ras-marques/ImmersiveGloves/CustomPCBs/InDevelopment/tundraIOExpansion/StencilJig/StencilBottom.stl

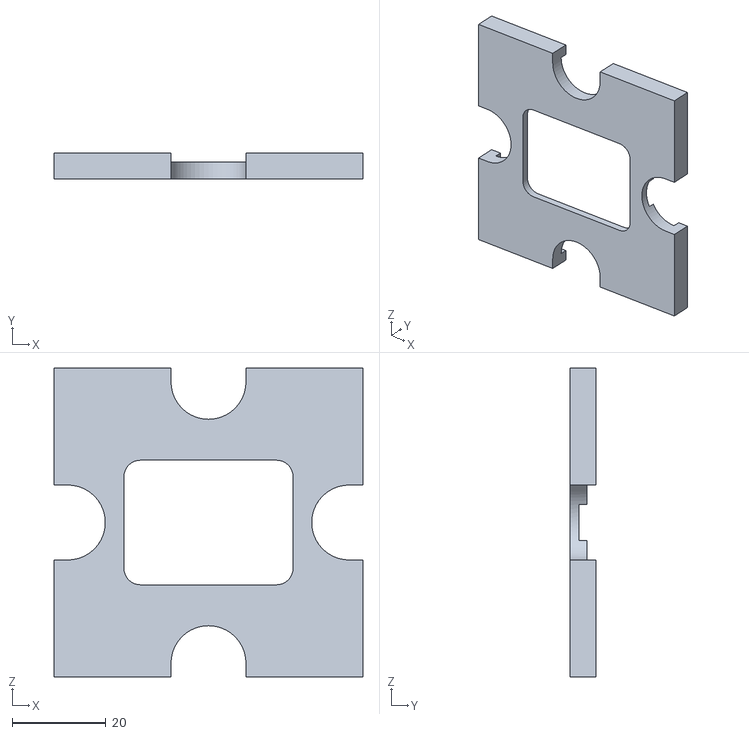
[picture p21: CAD file, 2024-01-13]
CustomPCBs/InDevelopment/tundraIOExpansion/StencilJig/StencilBottom.stl
66.0 x 5.65 x 66.0
