ras-marques/ImmersiveGloves/3DPrintingFiles/ReadyToTest/BackPlate/BackPlate.stl

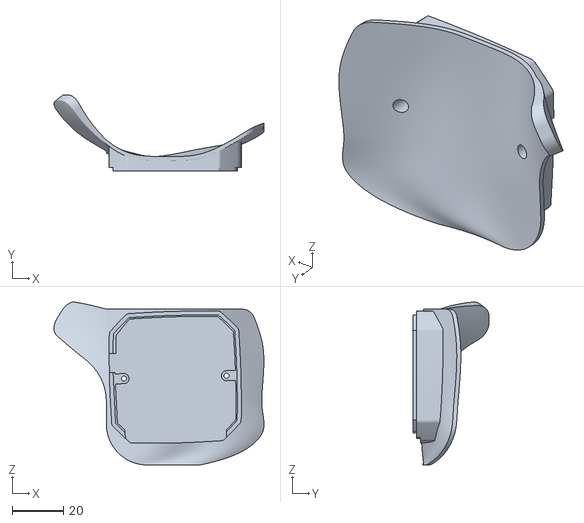
[picture p22: CAD file, 2023-12-02]
3DPrintingFiles/ReadyToTest/BackPlate/BackPlate.stl
82.0 x 29.8 x 63.7
