ras-marques/ImmersiveGloves/CustomPCBs/ComponentLibraries/3dmodels/6-TSOP.STEP

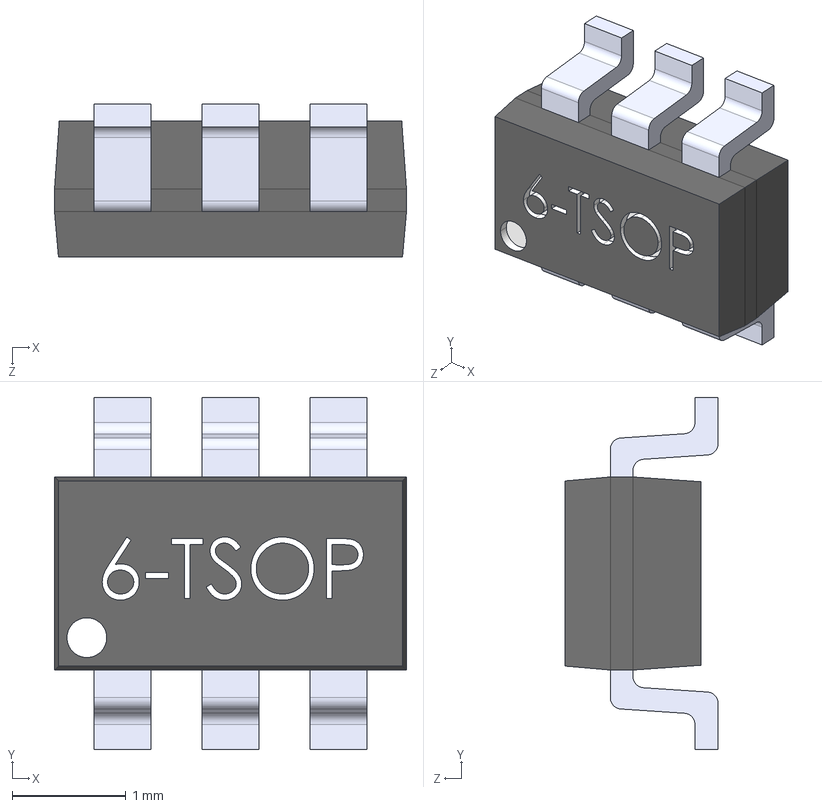
[picture p23: CAD file, 2024-02-26]
CustomPCBs/ComponentLibraries/3dmodels/6-TSOP.STEP
3.10 x 3.10 x 1.35 mm
