ras-marques/ImmersiveGloves/3DPrintingFiles/ReadyToTest/BackPlate/IMUHardPoint.stl

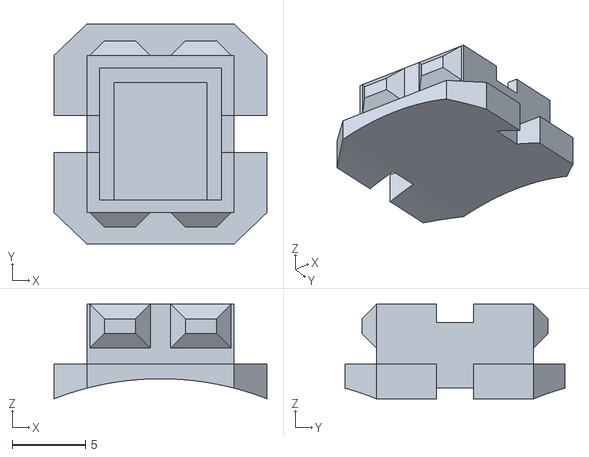
[picture p24: CAD file, 2023-12-02]
3DPrintingFiles/ReadyToTest/BackPlate/IMUHardPoint.stl
14.6 x 15.0 x 6.48
