ras-marques/ImmersiveGloves/CustomPCBs/ComponentLibraries/3dmodels/BSS138BKS,115.stp

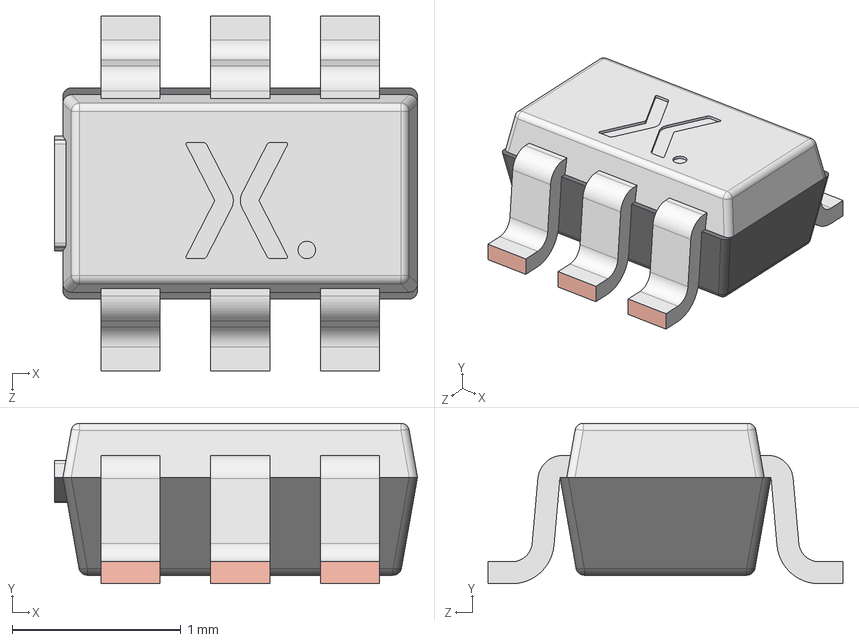
[picture p25: CAD file, 2024-02-26]
CustomPCBs/ComponentLibraries/3dmodels/BSS138BKS,115.stp
2.15 x 0.95 x 2.10 mm
SOT353 Lower body
SOT353 Lead x 6
SOT353 Upper body
