ras-marques/ImmersiveGloves/CustomPCBs/ComponentLibraries/3dmodels/ICM-20948.step

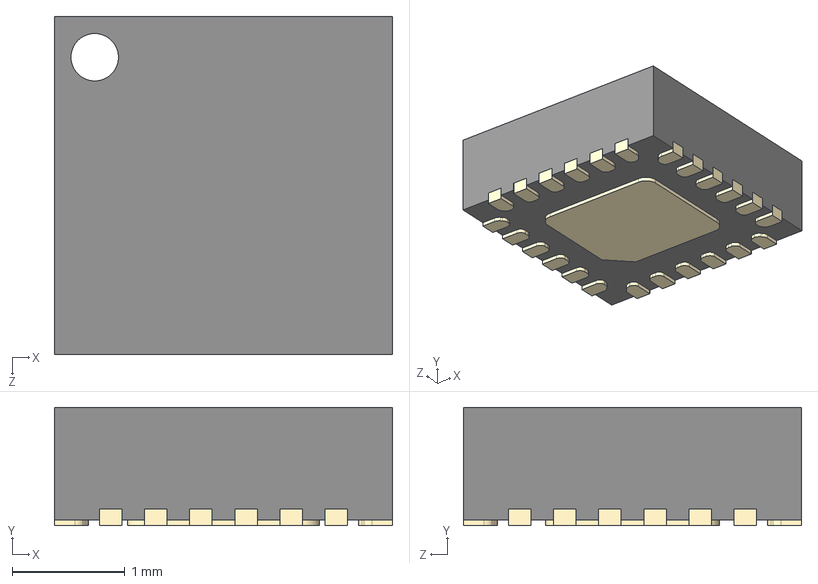
[picture p26: CAD file, 2024-02-26]
CustomPCBs/ComponentLibraries/3dmodels/ICM-20948.step
3.00 x 1.05 x 3.00 mm
