ras-marques/ImmersiveGloves/CustomPCBs/ComponentLibraries/3dmodels/User Library-SOT23-3.step

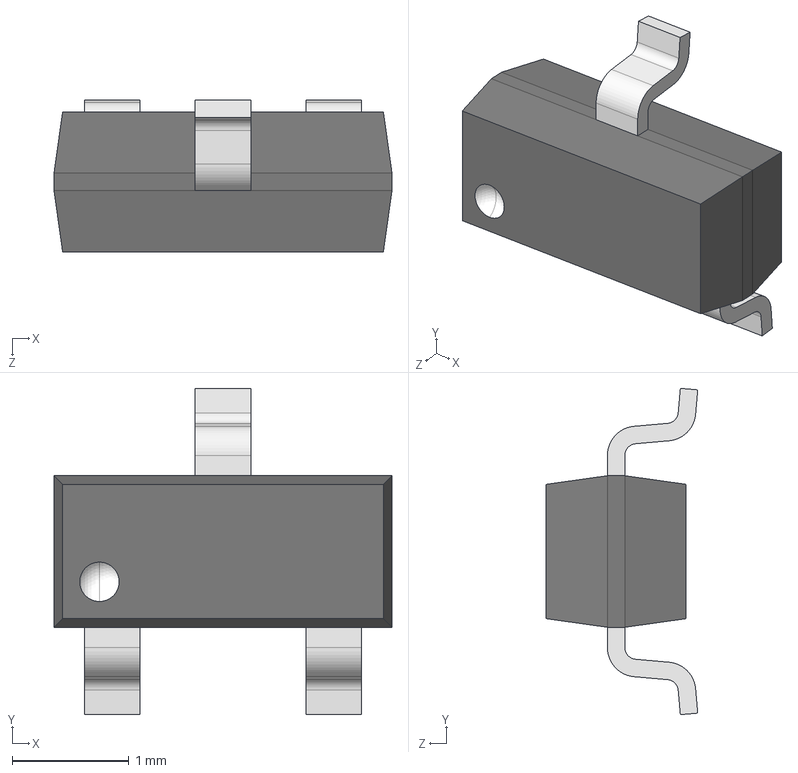
[picture p27: CAD file, 2024-02-26]
CustomPCBs/ComponentLibraries/3dmodels/User Library-SOT23-3.step
2.90 x 2.80 x 1.30 mm
