ras-marques/ImmersiveGloves/CustomPCBs/ComponentLibraries/3dmodels/User Library-TSSOP-6 (SOT-23-6 PITCH 0_65).STEP

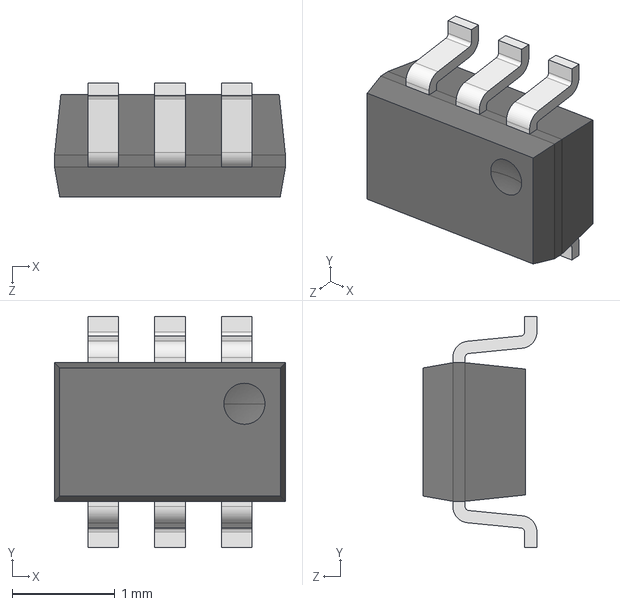
[picture p28: CAD file, 2024-02-26]
CustomPCBs/ComponentLibraries/3dmodels/User Library-TSSOP-6 (SOT-23-6 PITCH 0_65).STEP
2.25 x 2.25 x 1.11 mm
pin_TSSOP_tssop6_1 x 6
body_TSSOP-6_TSSOP5_1
