ras-marques/ImmersiveGloves/CustomPCBs/ComponentLibraries/3dmodels/HMC5883L-TR.step

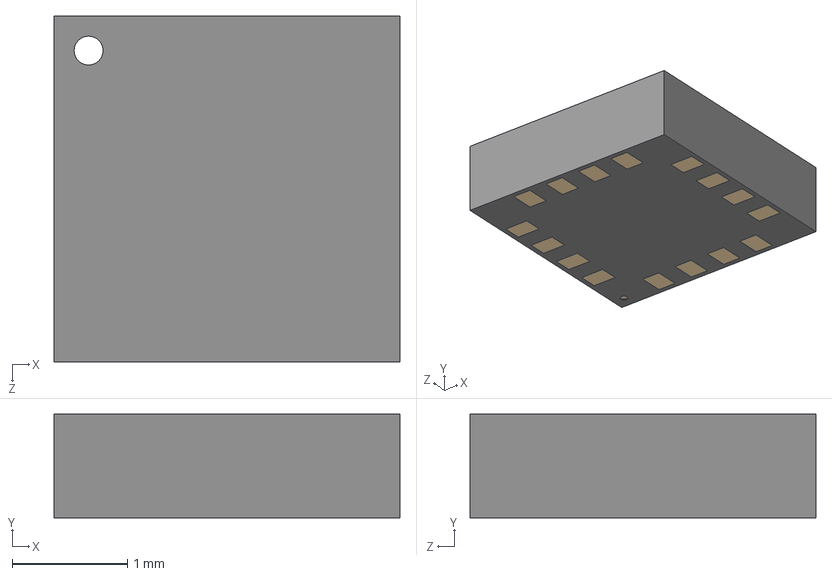
[picture p29: CAD file, 2024-02-26]
CustomPCBs/ComponentLibraries/3dmodels/HMC5883L-TR.step
3.00 x 0.9 x 3.00 mm
