ras-marques/ImmersiveGloves/CustomPCBs/ComponentLibraries/3dmodels/BSS138W-7-F.step

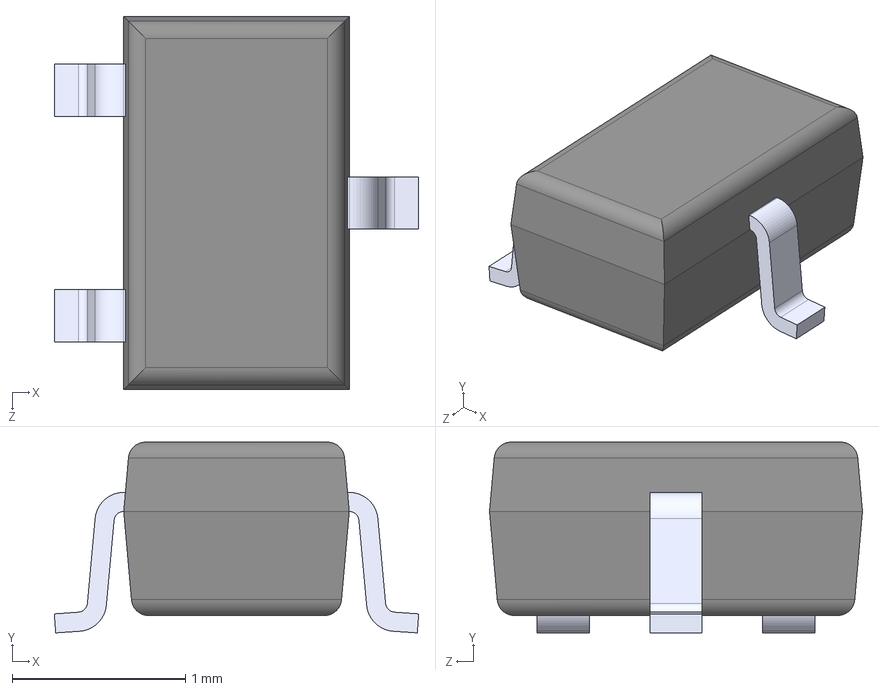
[picture p30: CAD file, 2024-02-25]
CustomPCBs/ComponentLibraries/3dmodels/BSS138W-7-F.step
2.10 x 1.10 x 2.15 mm
