ras-marques/ImmersiveGloves/CustomPCBs/ComponentLibraries/3dmodels/SM04B-SRSS-TB.STEP

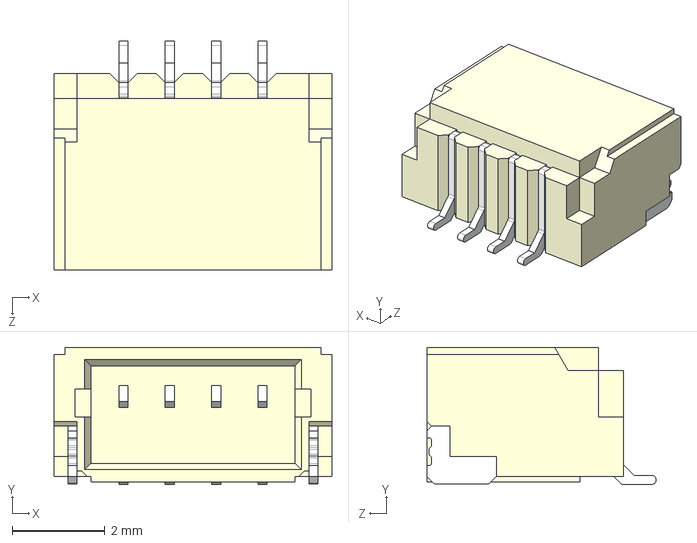
[picture p31: CAD file, 2024-02-16]
CustomPCBs/ComponentLibraries/3dmodels/SM04B-SRSS-TB.STEP
6.00 x 2.96 x 4.95 mm
