ras-marques/ImmersiveGloves/CustomPCBs/ComponentLibraries/3dmodels/LGA14-L_2P59X3P1X0P5_STM.step

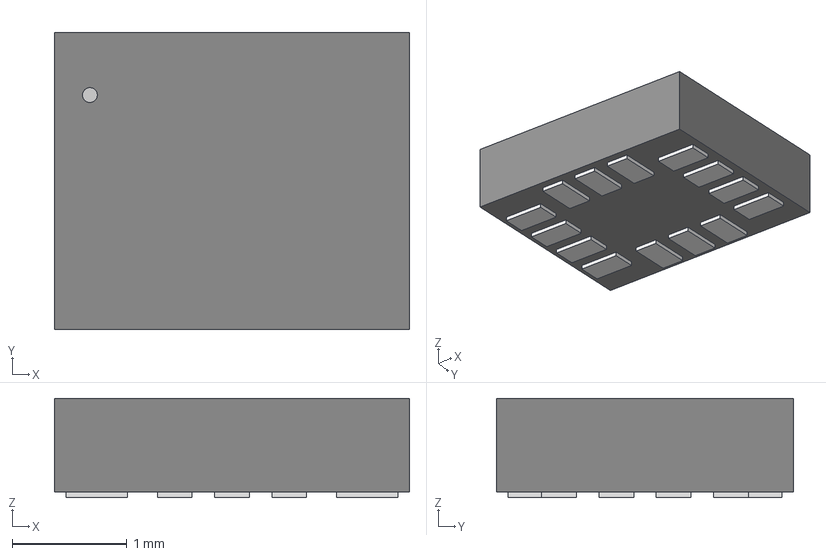
[picture p32: CAD file, 2024-02-16]
CustomPCBs/ComponentLibraries/3dmodels/LGA14-L_2P59X3P1X0P5_STM.step
3.10 x 2.59 x 0.866 mm
