ras-marques/ImmersiveGloves/rp2040Firmware/code.py

import array
import board
import busio
from adafruit_bno08x.i2c import BNO08X_I2C
from adafruit_bno08x import BNO_REPORT_LINEAR_ACCELERATION   # gives the acceleration with the gravity removed
from adafruit_bno08x import BNO_REPORT_ROTATION_VECTOR       # gives a quaternion from sensor fusion, including the magnetometer data

from adafruit_bno08x import BNO_REPORT_ACCELEROMETER
from adafruit_bno08x import BNO_REPORT_MAGNETOMETER
from adafruit_bno08x import BNO_REPORT_GYROSCOPE

# import pyquaternion
from ulab import numpy as np
import time
import rp2pio
import adafruit_pioasm
import bitbangio
import digitalio
import usb_cdc

serial = usb_cdc.data

assembled = adafruit_pioasm.assemble("""
.program spi_slave
.wrap_target:
    set x, 31
    pull
loop:
    wait 0 pin 1
    wait 0 pin 2
    out pins 1
    wait 1 pin 2
    jmp x-- loop
.wrap
""")

sm = rp2pio.StateMachine(
    assembled,
    frequency=0,
    first_out_pin=board.GP15,
    out_pin_count=1,
    first_in_pin=board.GP12,
    in_pin_count=3,
    out_shift_right=False
)

print(sm.frequency)

# confirmed ok
class Quaternion:
    def __init__(self, w, x, y, z):
        self.w = w
        self.x = x
        self.y = y
        self.z = z
    
    def printMe(self):
        print(str(self.w) + " " + str(self.x) + " " + str(self.y) + " " + str(self.z))
    
    def rotateBy(rotationQuaternion):
        return quaternion_multiply(rotationQuaternion, self)
    
    def getRelativeTo(referenceQuaternion):
        return quaternion_multiply(referenceQuaternion, quaternion_conjugate(self))
        

# confirmed ok
def quaternion_conjugate(q):
    return Quaternion(q.w, -q.x, -q.y, -q.z)

# confirmed ok
def quaternion_multiply(q1, q2):
    w1, x1, y1, z1 = q1.w, q1.x, q1.y, q1.z
    w2, x2, y2, z2 = q2.w, q2.x, q2.y, q2.z

    # Calculate the resulting quaternion components
    w = w1 * w2 - x1 * x2 - y1 * y2 - z1 * z2
    x = w1 * x2 + x1 * w2 + y1 * z2 - z1 * y2
    y = w1 * y2 - x1 * z2 + y1 * w2 + z1 * x2
    z = w1 * z2 + x1 * y2 - y1 * x2 + z1 * w2

    return Quaternion(w, x, y, z)

def getCurl(q):
    return np.arctan2(2 * (q.x * q.w - q.y * q.z), 1 - 2 * (q.x * q.x + q.y * q.y))
def getSplay(q):
    return np.arctan2(2 * (q.x * q.y + q.z * q.w), 1 - 2 * (q.y * q.y + q.z * q.z))
def getRoll(q):
    return np.arctan2(2 * (q.y * q.z + q.w * q.x), 1 - 2 * (q.x * q.x + q.y * q.y))

def quaternion_rotation_matrix(Q):
    """
    Covert a quaternion into a full three-dimensional rotation matrix.
 
    Input
    :param Q: A 4 element array representing the quaternion (q0,q1,q2,q3) 
 
    Output
    :return: A 3x3 element matrix representing the full 3D rotation matrix. 
             This rotation matrix converts a point in the local reference 
             frame to a point in the global reference frame.
    """
    # Extract the values from Q
    q0 = Q.w
    q1 = Q.x
    q2 = Q.y
    q3 = Q.z
     
    # First row of the rotation matrix
    r00 = 2 * (q0 * q0 + q1 * q1) - 1
    r01 = 2 * (q1 * q2 - q0 * q3)
    r02 = 2 * (q1 * q3 + q0 * q2)
     
    # Second row of the rotation matrix
    r10 = 2 * (q1 * q2 + q0 * q3)
    r11 = 2 * (q0 * q0 + q2 * q2) - 1
    r12 = 2 * (q2 * q3 - q0 * q1)
     
    # Third row of the rotation matrix
    r20 = 2 * (q1 * q3 - q0 * q2)
    r21 = 2 * (q2 * q3 + q0 * q1)
    r22 = 2 * (q0 * q0 + q3 * q3) - 1
     
    # 3x3 rotation matrix
    rot_matrix = np.array([[r00, r01, r02],
                           [r10, r11, r12],
                           [r20, r21, r22]])
                            
    return rot_matrix

def rotationMatrixToEulerAngles(R) :
    sy = np.sqrt(R[0,0] * R[0,0] +  R[1,0] * R[1,0])
 
    singular = sy < 1e-6
 
    if  not singular :
        x = np.arctan2(R[2,1] , R[2,2])
        y = np.arctan2(-R[2,0], sy)
        z = np.arctan2(R[1,0], R[0,0])
    else :
        x = np.arctan2(-R[1,2], R[1,1])
        y = np.arctan2(-R[2,0], sy)
        z = 0
 
    return np.array([x*180/3.14, y*180/3.14, z*180/3.14])

def quaternionFromAngle(angle, axis):
    # angle is in radians, x axis is 0, y axis is 1, z axis is 2
    if axis == 0:
        return Quaternion(np.cos(angle/2),np.sin(angle/2),0,0)
    if axis == 1:
        return Quaternion(np.cos(angle/2),0,np.sin(angle/2),0)
    if axis == 2:
        return Quaternion(np.cos(angle/2),0,0,np.sin(angle/2))

thumbActive = False
indexActive = False
middleActive = False
ringActive = False
pinkyActive = False

i2c_0 = 0
i2c_1 = 0
i2c_2 = 0
i2c_3 = 0
i2c_4 = 0
i2c_5 = 0
bnoRef = 0
bnoThumb = 0
bnoIndex = 0
bnoMiddle = 0
bnoRing = 0
bnoPinky = 0

#i2c_0 = busio.I2C(board.GP5, board.GP4, frequency = 400000, timeout = 8000)
#i2c_1 = busio.I2C(board.GP7, board.GP6, frequency = 400000, timeout = 8000)

# bnoRef = BNO08X_I2C(i2c_0, None, 0x4A, False)
# bnoRef.enable_feature(BNO_REPORT_ROTATION_VECTOR)
# bnoRef.enable_feature(BNO_REPORT_LINEAR_ACCELERATION)

#bnoRef.enable_feature(BNO_REPORT_ACCELEROMETER)
#bnoRef.enable_feature(BNO_REPORT_GYROSCOPE)
#bnoRef.enable_feature(BNO_REPORT_MAGNETOMETER)

if thumbActive:
    bnoThumb = BNO08X_I2C(i2c_0, None, 0x4A)
    bnoThumb.enable_feature(BNO_REPORT_ROTATION_VECTOR)
    bnoThumb.enable_feature(BNO_REPORT_LINEAR_ACCELERATION)
if indexActive:
    bnoIndex = BNO08X_I2C(i2c_1, None, 0x4B)
    bnoIndex.enable_feature(BNO_REPORT_ROTATION_VECTOR)
if middleActive:
    bnoMiddle = BNO08X_I2C(i2c_1, None, 0x4A)
    bnoMiddle.enable_feature(BNO_REPORT_ROTATION_VECTOR)
if ringActive:
    i2c_2_bitbanged = bitbangio.I2C(board.GP4, board.GP5, frequency = 400000, timeout = 8000)
    bnoRing = BNO08X_I2C(i2c_2_bitbanged, None, 0x4B)
    bnoRing.enable_feature(BNO_REPORT_ROTATION_VECTOR)
if pinkyActive:
    i2c_3_bitbanged = bitbangio.I2C(board.GP0, board.GP1, frequency = 400000, timeout = 8000)
    bnoPinky = BNO08X_I2C(i2c_3_bitbanged, None, 0x4B)
    bnoPinky.enable_feature(BNO_REPORT_ROTATION_VECTOR)

spi_protocol_rev = 1
frame_id = 0
report_mode = 3         # MI_PROTOCOL_REVISION_GENERIC
status = 0              # 0 normal, 1 bootloader
input_data_length = 15  # 15 bytes, 120 bits, see a bit below
backchannel_length = 0  # only for RX, probably for haptics that I am not using yet (YET!)
event_data_length = 0   # only for RX, probably for haptics that I am not using yet (YET!)
reserved = 0

thumb_axis = 0             # 10  0
index_axis = 512             # 10  10
middle_axis = 512            # 10  20
ring_axis = 0              # 10  30
pinky_axis = 0             # 10  40
thumb_splay_axis = 0       # 10  50
index_splay_axis = 0       # 10  60
middle_splay_axis = 0      # 10  70
ring_splay_axis = 0        # 10  80
pinky_splay_axis = 0       # 10  90
joystick_x = 0             # 10  100
joystick_y = 0             # 10  110
joystickIsEnabled = False  #  1  120

# 120 bits are 15 bytes

first_header_32bits  = (spi_protocol_rev << 24) + (frame_id << 16) + (report_mode << 8) + (status << 0)
second_header_32bits = (input_data_length << 24) + (backchannel_length << 16) + (event_data_length << 8) + (reserved << 0)

# during my tests, for some reason the finger curl was only working if the reference IMU quaternion is the one in the definition below.
# so for everything to work, I define the quaternion below and rotate everything to this coordinate frame.
# for that, I take the relative quaternion from the reference IMU to this quaternion and then use this relative quaternion to rotate every IMU into this reference frame
# then, finally, I do all my calculations.
handQuaternionThatWorks = Quaternion(np.sqrt(2)/2,0,0,-np.sqrt(2)/2)

# for the thumb movement, I needed to get a first neutral position from which to take rotations
# the relative rotation to the reference IMU is represented by the quaternion below, taken experimentally
thumbNeutralToHandQuaternion = Quaternion(0.623351, 0.0097146, 0.754592, 0.204794)

# for the joystick emulation, I need a neutral rotation from which to take roll and pitch and map it into joystick values
# the relative rotation to the reference IMU is represented by the quaternion below, taken experimentally
thumbNeutralJoystickToHandQuaternion = Quaternion(0.586889, -0.168701, 0.779479, 0.140207)

# for splay, I took measurements of the results of my calculations and the splay angle results are as follows:
# finger   min  rest  max
# index    -22   18    35
# middle   -11    4    28
# ring     -14   -5    14
# pinky    -40  -25    -2

refAccelTime = time.monotonic()
thumbAccelTime = time.monotonic()

joystick_enabled = digitalio.DigitalInOut(board.GP10)
joystick_enabled.pull = digitalio.Pull.UP

#################################
# SENSOR FUSION BENCHMARK START #
#################################
def TO_RAD(x):
    return x * 0.01745329252 # *pi/180
def TO_DEG(x):
    return x * 57.2957795131 # *180/pi

# Multiply two 3x3 matrices: out = a * b
def Matrix_Multiply(a, b):
    return np.dot(a,b)

# Adds two vectors
def Vector_Add(v1, v2):
    return v1+v2

# Computes the dot product of two vectors
def Vector_Dot_Product(v1, v2):
    return np.dot(v1,v2)

def Vector_Cross_Product(v1, v2):
    out = np.empty([3])
    out[0] = (v1[1] * v2[2]) - (v1[2] * v2[1])
    out[1] = (v1[2] * v2[0]) - (v1[0] * v2[2])
    out[2] = (v1[0] * v2[1]) - (v1[1] * v2[0])
    return out

# Multiply the vector by a scalar
def Vector_Scale(v, scale):
    return v*scale
# 
# # Init rotation matrix using euler angles
# def init_rotation_matrix(yaw, pitch, roll):
#     m = np.empty([3, 3])
#     c1 = np.cos(roll)
#     s1 = np.sin(roll)
#     c2 = np.cos(pitch)
#     s2 = np.sin(pitch)
#     c3 = np.cos(yaw)
#     s3 = np.sin(yaw)
#     # Euler angles, right-handed, intrinsic, XYZ convention
#     # (which means: rotate around body axes Z, Y', X'')
#     m[0][0] = c2 * c3
#     m[0][1] = c3 * s1 * s2 - c1 * s3
#     m[0][2] = s1 * s3 + c1 * c3 * s2
# 
#     m[1][0] = c2 * s3
#     m[1][1] = c1 * c3 + s1 * s2 * s3
#     m[1][2] = c1 * s2 * s3 - c3 * s1
# 
#     m[2][0] = -s2
#     m[2][1] = c2 * s1
#     m[2][2] = c1 * c2
# 
#     return m
# 
# def read_sensors():
#     global accel_xyz
#     global gyro_xyz
#     global magn_xyz
#     accel_xyz = bnoRef.acceleration
#     gyro_xyz = bnoRef.gyro
#     magn_xyz = bnoRef.magnetic
# 
# def reset_sensor_fusion():
#     global DCM_Matrix
#     global pitch
#     global roll
#     global MAG_Heading
#     global yaw
#     global DCM_Matrix
#     global timer
# 
#     xAxis = [1, 0, 0]
# 
#     read_sensors()
#     timer = time.monotonic()
# 
#     # GET PITCH
#     # Using y-z-plane-component/x-component of gravity vector
#     pitch = -np.arctan2(accel_xyz[0], np.sqrt(accel_xyz[1] * accel_xyz[1] + accel_xyz[2] * accel_xyz[2]))
#     # GET ROLL
#     # Compensate pitch of gravity vector
#     temp1 = Vector_Cross_Product(accel_xyz, xAxis)
#     temp2 = Vector_Cross_Product(xAxis, temp1)
#     # Normally using x-z-plane-component/y-component of compensated gravity vector
#     # roll = atan2(temp2[1], sqrt(temp2[0] * temp2[0] + temp2[2] * temp2[2]))
#     # Since we compensated for pitch, x-z-plane-component equals z-component:
#     roll = np.arctan2(temp2[1], temp2[2])
# 
#     # GET YAW
#     Compass_Heading()
#     yaw = MAG_Heading
# 
#     # Init rotation matrix
#     DCM_Matrix = init_rotation_matrix(yaw, pitch, roll)
# 
# def compensate_gyro_offset():
#     global gyro_xyz
#     gyro_xyz = list(gyro_xyz)
#     gyro_xyz[0] = gyro_xyz[0] - GYRO_AVERAGE_OFFSET_X
#     gyro_xyz[1] = gyro_xyz[1] - GYRO_AVERAGE_OFFSET_Y
#     gyro_xyz[2] = gyro_xyz[2] - GYRO_AVERAGE_OFFSET_Z
# 
# def Compass_Heading():
#     global MAG_Heading
#     
#     cos_roll = np.cos(roll)
#     sin_roll = np.sin(roll)
#     cos_pitch = np.cos(pitch)
#     sin_pitch = np.sin(pitch)
# 
#     # Tilt compensated magnetic field X
#     mag_x = magn_xyz[0] * cos_pitch + magn_xyz[1] * sin_roll * sin_pitch + magn_xyz[2] * cos_roll * sin_pitch
#     # Tilt compensated magnetic field Y
#     mag_y = magn_xyz[1] * cos_roll - magn_xyz[2] * sin_roll
#     # Magnetic Heading
#     MAG_Heading = np.arctan2(-mag_y, mag_x)
#     # MAG_Heading = 0
# 
# def Matrix_update():
#     global Omega
#     global Omega_Vector
#     global gyro_xyz
#     global DCM_Matrix
#     global Temporary_Matrix
#     
#     # gyro_xyz[0] = TO_RAD(gyro_xyz[0]*GYRO_GAIN)
#     # gyro_xyz[1] = TO_RAD(gyro_xyz[1]*GYRO_GAIN)
#     # gyro_xyz[2] = TO_RAD(gyro_xyz[2]*GYRO_GAIN)
#     # gyro_xyz[0] = TO_RAD(gyro_xyz[0])
#     # gyro_xyz[1] = TO_RAD(gyro_xyz[1])
#     # gyro_xyz[2] = TO_RAD(gyro_xyz[2])
# 
#     Update_Matrix = np.empty([3,3])
# 
#     Omega = Vector_Add(gyro_xyz, Omega_I) # adding proportional term calculated in Drift_Correction()
#     Omega_Vector = Vector_Add(Omega, Omega_P) # adding Integrator term calculated in Drift_Correction()
# 
#     #Ver equacoes 15 16 e 17 no paper Direction Cosine Matrix IMU: Theory - William Premerlani and Paul Bizard
#     #Omega_Vector e o vetor do giroscopio com correcao ao drift
#     Update_Matrix[0][0] =0
#     Update_Matrix[0][1]=-G_Dt*Omega_Vector[2] # -z
#     Update_Matrix[0][2]=G_Dt*Omega_Vector[1] # y
#     Update_Matrix[1][0]=G_Dt*Omega_Vector[2] # z
#     Update_Matrix[1][1]=0
#     Update_Matrix[1][2]=-G_Dt*Omega_Vector[0] # -x
#     Update_Matrix[2][0]=-G_Dt*Omega_Vector[1] #-y
#     Update_Matrix[2][1]=G_Dt*Omega_Vector[0] # x
#     Update_Matrix[2][2]=0
# 
#     Temporary_Matrix = Matrix_Multiply(DCM_Matrix,Update_Matrix)
#     DCM_Matrix = DCM_Matrix + Temporary_Matrix
# 
# def Normalize():  # confirmei pelo paper e esta bem
#     temporary = np.empty([3, 3])
# 
#     error = -Vector_Dot_Product(DCM_Matrix[0], DCM_Matrix[1]) * .5  # eq.19
# 
#     temporary[0] = Vector_Scale(DCM_Matrix[1], error)  # eq.19
#     temporary[1] = Vector_Scale(DCM_Matrix[0], error)  # eq.19
# 
#     temporary[0] = Vector_Add(temporary[0], DCM_Matrix[0])  # eq.19
#     temporary[1] = Vector_Add(temporary[1], DCM_Matrix[1])  # eq.19
# 
#     temporary[2] = Vector_Cross_Product(temporary[0], temporary[1])  # c= a x b //eq.20
# 
#     renorm = .5 * (3 - Vector_Dot_Product(temporary[0], temporary[0]))  # eq.21
#     DCM_Matrix[0] = Vector_Scale(temporary[0], renorm)
# 
#     renorm = .5 * (3 - Vector_Dot_Product(temporary[1], temporary[1]))  # eq.21
#     DCM_Matrix[1] = Vector_Scale(temporary[1], renorm)
# 
#     renorm = .5 * (3 - Vector_Dot_Product(temporary[2], temporary[2]))  # eq.21
#     DCM_Matrix[2] = Vector_Scale(temporary[2], renorm)
# 
# def Drift_correction():  # AINDA NAO ACABEI DE PORTAR PARA PYTHON!!!
#     # Global variables
#     global Omega_P
#     global Omega_I
#     global errorRollPitch
#     global errorYaw
#     
#     # Compensation the Roll, Pitch and Yaw drift.
#     # Scaled_Omega_P
#     # Scaled_Omega_I
#     # Accel_magnitude
#     # Accel_weight
# 
#     # *****Roll and Pitch***************
# 
#     # Calculate the magnitude of the accelerometer vector
#     Accel_magnitude = np.sqrt(accel_xyz[0] * accel_xyz[0] + accel_xyz[1] * accel_xyz[1] + accel_xyz[2] * accel_xyz[2])
# 
#     # Dynamic weighting of accelerometer info (reliability filter)
#     # Weight for accelerometer info (<0.5G = 0.0, 1G = 1.0 , >1.5G = 0.0)
#     accel_test = 1 - 2 * abs(1 - Accel_magnitude)
#     if accel_test > 1:
#         Accel_weight = 1
#     elif accel_test < 0:
#         Accel_weight = 0
#     else:
#         Accel_weight = accel_test
# 
#     errorRollPitch = Vector_Cross_Product(accel_xyz, DCM_Matrix[2])  # adjust the ground of reference
#     Omega_P = Vector_Scale(errorRollPitch, Kp_ROLLPITCH * Accel_weight)
# 
#     Scaled_Omega_I = Vector_Scale(errorRollPitch, Ki_ROLLPITCH * Accel_weight)
#     Omega_I = Vector_Add(Omega_I, Scaled_Omega_I)
# 
#     # *****YAW***************
#     # We make the gyro YAW drift correction based on compass magnetic heading
# 
#     mag_heading_x = np.cos(MAG_Heading)
#     mag_heading_y = np.sin(MAG_Heading)
#     errorCourse = (DCM_Matrix[0][0] * mag_heading_y) - (DCM_Matrix[1][0] * mag_heading_x)  # Calculating YAW error
#     errorYaw = Vector_Scale(DCM_Matrix[2], errorCourse)  # Applys the yaw correction to the XYZ rotation of the aircraft, depeding the position.
# 
#     Scaled_Omega_P = Vector_Scale(errorYaw, Kp_YAW)  # .01proportional of YAW.
#     Omega_P = Vector_Add(Omega_P, Scaled_Omega_P)  # Adding  Proportional.
# 
#     Scaled_Omega_I = Vector_Scale(errorYaw, Ki_YAW)  # .00001Integrator
#     Omega_I = Vector_Add(Omega_I, Scaled_Omega_I)  # adding integrator to the Omega_I
# 
# def Euler_angles():
#     global pitch
#     global roll
#     global yaw
# 
#     global pitch_deg
#     global roll_deg
#     global yaw_deg
#     
#     # Vem das identidades trigonometricas da matriz de rotacao: Direct Cosine Matrix (DCM)
#     # Ja confirmei, esta certo, nao perder tempo aqui, ver como a DCM_Matrix e construida antes
#     pitch = -np.asin(DCM_Matrix[2][0])
#     roll = np.arctan2(DCM_Matrix[2][1],DCM_Matrix[2][2])
#     yaw = np.arctan2(DCM_Matrix[1][0],DCM_Matrix[0][0])
# 
#     pitch_deg = TO_DEG(pitch)
#     roll_deg = TO_DEG(roll)
#     yaw_deg = TO_DEG(yaw)
# 
# def print_angles():
#     print("yaw   = %.0f" % yaw_deg)
#     print("pitch = %.0f" % pitch_deg)
#     print("roll  = %.0f" % roll_deg)
#     print("")
# 
# accel_xyz = np.empty([3])
# gyro_xyz = np.empty([3])
# magn_xyz = np.empty([3])
# MAG_Heading = 0
# 
# gyro_offset = np.empty([3])
# for i in range(0, 63):
#     gyro_result = bnoRef.gyro
#     gyro_offset[0] += gyro_result[0]
#     gyro_offset[1] += gyro_result[1]
#     gyro_offset[2] += gyro_result[2]
# 
# GYRO_AVERAGE_OFFSET_X = gyro_offset[0] * 0.015625  # 1/64
# GYRO_AVERAGE_OFFSET_Y = gyro_offset[1] * 0.015625  # 1/64
# GYRO_AVERAGE_OFFSET_Z = gyro_offset[2] * 0.015625  # 1/64
# 
# #DCM parameters
# Kp_ROLLPITCH = 0.02
# Ki_ROLLPITCH = 0.00002
# Kp_YAW = 1.2
# Ki_YAW = 0.00002
# 
# # DCM variables
# MAG_Heading = 0
# #Accel_Vector = np.empty([3]) # Store the acceleration in a vector
# #Gyro_Vector = np.empty([3]) # Store the gyros turn rate in a vector
# Omega_Vector = np.zeros(3) # Corrected Gyro_Vector data
# Omega_P = np.zeros(3) # Omega Proportional correction
# Omega_I = np.zeros(3) # Omega Integrator
# Omega = np.zeros(3)
# errorRollPitch = np.empty([3])
# errorYaw = np.empty([3])
# DCM_Matrix = np.array([[1,0,0],[0,1,0],[0,0,1]])
# Temporary_Matrix = np.empty([3,3])
# 
# reset_sensor_fusion()

timer = time.monotonic_ns()/1000000
# while True:
#     if time.monotonic_ns()/1000000 - timer >= 20:  # Main loop runs at 50Hz
#         timer_old = timer
#         timer = time.monotonic_ns()/1000000
#         if timer > timer_old:
#             G_Dt = (timer - timer_old) / 1000.0  # Real time of loop run. We use this on the DCM algorithm (gyro integration time)
#         else:
#             G_Dt = 0
#         
#         read_sensors()
#         secondTimer = time.monotonic_ns()/1000000
#         
#         for i in range(6):        
#             #pitch_test = -np.arctan2(accel_xyz[0], np.sqrt(accel_xyz[1] * accel_xyz[1] + accel_xyz[2] * accel_xyz[2]))
#             #print TO_DEG(pitch_test)
#             #print_accel()
# 
#             compensate_gyro_offset()
#             #compensate_sensor_errors()
# 
#             #print_gyro()
# 
#             # Run DCM algorithm
#             if magn_xyz[0] != 0 and magn_xyz[0] != 0 and magn_xyz[0] != 0:
#                 Compass_Heading()  # Calculate magnetic heading
#                 #print(MAG_Heading)
#             Matrix_update()
#             Normalize()
#             Drift_correction()
#             # ***
#             Euler_angles()
# 
#         #print_angles()
#         
#         print(time.monotonic_ns()/1000000 - secondTimer)

###############################
# SENSOR FUSION BENCHMARK END #
###############################

# while True:
#     handQuaternion = Quaternion(bnoRef.quaternion[3],bnoRef.quaternion[0],bnoRef.quaternion[1],bnoRef.quaternion[2])                    # get the reference IMU quaternion
#     handQuaternion.printMe()

thumbCurlUp = True
indexCurlUp = True
middleCurlUp = True
ringCurlUp = True
pinkyCurlUp = True

thumbSplayUp = True
indexSplayUp = True
middleSplayUp = True
ringSplayUp = True
pinkySplayUp = True

while True:
    # handQuaternion = Quaternion(bnoRef.quaternion[3],bnoRef.quaternion[0],bnoRef.quaternion[1],bnoRef.quaternion[2])                    # get the reference IMU quaternion
    # handQuaternion.printMe()
    # relativeQuaternion = quaternion_multiply(handQuaternionThatWorks, quaternion_conjugate(handQuaternion))                             # get the relative quaternion between the reference IMU quaternion and the coordinate frame where my calculations work
    # handQuaternion = quaternion_multiply(relativeQuaternion, handQuaternion)                                                            # rotate the handQuaternion to be in the coordinate frame where my calculations work
    #handQuaternion.printMe()

    if thumbActive:
        thumbQuaternion = Quaternion(bnoThumb.quaternion[3],bnoThumb.quaternion[0],bnoThumb.quaternion[1],bnoThumb.quaternion[2])       # get the thumb IMU quaternion
        thumbQuaternion = quaternion_multiply(relativeQuaternion, thumbQuaternion)                                                      # rotate the thumbQuaternion to be in the coordinate frame where my calculations work
        thumbQuaternionBackupForJoystick = thumbQuaternion
        
        # weirdly I don't need this, but don't know why
        thumbToHandQuaternion = quaternion_multiply(handQuaternion, quaternion_conjugate(thumbQuaternion))                              # get the relative quaternion between the reference IMU quaternion and the thumb IMU quaternion
        
        thumbQuaternion = quaternion_multiply(thumbNeutralToHandQuaternion, thumbQuaternion)                                            # rotate the relative quaternion between the reference IMU quaternion and the thumb IMU quaternion by the neutral thumb quaternion (is it? I don't know if I did exactly this, but it works)
        thumbCurlAmount = getCurl(thumbQuaternion)
        thumbAngle = int(thumbCurlAmount*180/3.14)
        thumb_axis = int(512+512*thumbAngle/90.)
        if thumb_axis < 0:
            thumb_axis = 0
        elif thumb_axis > 1023:
            thumb_axis = 1023
        #print(thumb_axis)
        
        thumbCurlQuaternion = quaternionFromAngle(thumbCurlAmount, 0)                                                                   # create a quaternion that represents just the amount of curl in the x axis
        thumbDecurledQuaternion = quaternion_multiply(thumbCurlQuaternion, thumbQuaternion)                                             # rotate the indexQuaternion by the curl angle in the x axis        
        thumbDecurledToNeutralQuaternion = quaternion_multiply(handQuaternion, quaternion_conjugate(thumbDecurledQuaternion))           # get the relative quaternion between the reference IMU quaternion and the quaternion representing the index IMU rotated back by the curl angle
        thumbSplayAmount = getSplay(thumbDecurledToNeutralQuaternion)                                                                   # get the splay angle in radians from the quaternion calculated above
        thumbSplayAngle = int(thumbSplayAmount*180/3.14)                                                                                # convert the splay angle to degrees
        thumb_splay_axis = int(512+512*thumbSplayAngle/42.)
        if thumb_splay_axis < 0:
            thumb_splay_axis = 0
        elif thumb_splay_axis > 1023:
            thumb_splay_axis = 1023
        #print(thumb_splay_axis)
        #thumbAccel_x, thumbAccel_y, thumbAccel_z = bnoThumb.linear_acceleration
        
        # inverted logic, this is when the joystick is enabled
        if not joystick_enabled.value:
            #if not joystickIsEnabled:
            #    thumbNeutralJoystickToHandQuaternion = thumbToHandQuaternion # fix this value on the top and don't reset it each time joystick is reenabled
            #thumbToHandQuaternion.printMe()
            
            thumbJoystickQuaternion = quaternion_multiply(thumbNeutralJoystickToHandQuaternion, thumbQuaternionBackupForJoystick) #thumbQuaternionBackupForJoystick.rotateBy(thumbNeutralJoystickToHandQuaternion)
            
            joystick_x_angleRadians = getRoll(thumbJoystickQuaternion)
            joystick_x_angleDegrees = (joystick_x_angleRadians*180/3.14)
            joystick_x = int((joystick_x_angleDegrees + 25)*1023/50)
            if joystick_x < 0:
                joystick_x = 0
            elif joystick_x > 1023:
                joystick_x = 1023
            
            joystick_y_angleRadians = getCurl(thumbJoystickQuaternion)
            joystick_y_angleDegrees = (joystick_y_angleRadians*180/3.14)
            joystick_y = int((joystick_y_angleDegrees + 25)*1023/50)
            if joystick_y < 0:
                joystick_y = 0
            elif joystick_y > 1023:
                joystick_y = 1023
            
            joystickIsEnabled = True
        else:
            joystick_x = 512
            joystick_y = 512
            
            joystickIsEnabled = False
        
        #print("x: " + str(joystick_x))
        #print("y: " + str(joystick_y))
        
    if indexActive:
        indexQuaternion = Quaternion(bnoIndex.quaternion[3],bnoIndex.quaternion[0],bnoIndex.quaternion[1],bnoIndex.quaternion[2])       # get the index IMU quaternion
        indexQuaternion = quaternion_multiply(relativeQuaternion, indexQuaternion)                                                      # rotate the indexQuaternion to be in the coordinate frame where my calculations work
        indexToHandQuaternion = quaternion_multiply(handQuaternion, quaternion_conjugate(indexQuaternion))                              # get the relative quaternion between the reference IMU quaternion and the index IMU quaternion
        indexCurlAmount = getCurl(indexToHandQuaternion)                                                                                # get the curl angle in radians from the quaternion calculated above
        indexAngle = int(indexCurlAmount*180/3.14)                                                                                      # convert the curl angle to degrees
        # remap the angle output in degrees to a value between 0 and 1023: the following calculations were a bit hacky when I implemented them and I didn't document them properly, still, they were based on observations of the outputs and you may be able to reverse engineer an explanation
        if indexAngle <= 0 and indexAngle >= -180:
            index_axis = int(682 * -indexAngle / 180)
        elif indexAngle <= 180 and indexAngle >= 90:
            index_axis = int(682 - (341 / 90) * (indexAngle - 180))
        
        indexCurlQuaternion = quaternionFromAngle(indexCurlAmount, 0)                                                                   # create a quaternion that represents just the amount of curl in the x axis
        indexDecurledQuaternion = quaternion_multiply(indexCurlQuaternion, indexQuaternion)                                             # rotate the indexQuaternion by the curl angle in the x axis
        indexDecurledToHandQuaternion = quaternion_multiply(handQuaternion, quaternion_conjugate(indexDecurledQuaternion))              # get the relative quaternion between the reference IMU quaternion and the quaternion representing the index IMU rotated back by the curl angle
        indexSplayAmount = getSplay(indexDecurledToHandQuaternion)                                                                      # get the splay angle in radians from the quaternion calculated above
        indexSplayAngle = int(indexSplayAmount*180/3.14)                                                                                # convert the splay angle to degrees
        #print(str(indexSplayAngle))
        # finger   min  rest  max
        # index    -22   18    35
        if indexSplayAngle <= 18:
            index_splay_axis = int(512+512*(indexSplayAngle-18)/40.)
        else:
            index_splay_axis = int(512+512*(indexSplayAngle-18)/17.)
        if index_splay_axis < 0:
            index_splay_axis = 0
        elif index_splay_axis > 1023:
            index_splay_axis = 1023
    
    if middleActive:
        middleQuaternion = Quaternion(bnoMiddle.quaternion[3],bnoMiddle.quaternion[0],bnoMiddle.quaternion[1],bnoMiddle.quaternion[2])  # get the middle IMU quaternion
        middleQuaternion = quaternion_multiply(relativeQuaternion, middleQuaternion)                                                    # rotate the middleQuaternion to be in the coordinate frame where my calculations work
        middleToHandQuaternion = quaternion_multiply(handQuaternion, quaternion_conjugate(middleQuaternion))                            # get the relative quaternion between the reference IMU quaternion and the middle IMU quaternion
        middleCurlAmount = getCurl(middleToHandQuaternion)                                                                              # get the curl angle in radians from the quaternion calculated above
        middleAngle = int(middleCurlAmount*180/3.14)                                                                                    # convert the curl angle to degrees
        # remap the angle output in degrees to a value between 0 and 1023: the following calculations were a bit hacky when I implemented them and I didn't document them properly, still, they were based on observations of the outputs and you may be able to reverse engineer an explanation
        if middleAngle <= 0 and middleAngle >= -180:
            middle_axis = int(682 * -middleAngle / 180)
        elif middleAngle <= 180 and middleAngle >= 90:
            middle_axis = int(682 - (341 / 90) * (middleAngle - 180))
            
        middleCurlQuaternion = quaternionFromAngle(middleCurlAmount, 0)                                                                 # create a quaternion that represents just the amount of curl in the x axis
        middleDecurledQuaternion = quaternion_multiply(middleCurlQuaternion, middleQuaternion)                                          # rotate the middleQuaternion by the curl angle in the x axis
        middleDecurledToHandQuaternion = quaternion_multiply(handQuaternion, quaternion_conjugate(middleDecurledQuaternion))            # get the relative quaternion between the reference IMU quaternion and the quaternion representing the middle IMU rotated back by the curl angle
        middleSplayAmount = getSplay(middleDecurledToHandQuaternion)                                                                    # get the splay angle in radians from the quaternion calculated above
        middleSplayAngle = int(middleSplayAmount*180/3.14)                                                                              # convert the splay angle to degrees
        # finger   min  rest  max
        # middle   -11    4    28
        if middleSplayAngle <= 4:
            middle_splay_axis = int(512+512*(middleSplayAngle-4)/15.)
        else:
            middle_splay_axis = int(512+512*(middleSplayAngle-4)/24.)
        if middle_splay_axis < 0:
            middle_splay_axis = 0
        elif middle_splay_axis > 1023:
            middle_splay_axis = 1023
    
    if ringActive:
        ringQuaternion = Quaternion(bnoRing.quaternion[3],bnoRing.quaternion[0],bnoRing.quaternion[1],bnoRing.quaternion[2])            # get the ring IMU quaternion
        ringQuaternion = quaternion_multiply(relativeQuaternion, ringQuaternion)                                                        # rotate the ringQuaternion to be in the coordinate frame where my calculations work
        ringToHandQuaternion = quaternion_multiply(handQuaternion, quaternion_conjugate(ringQuaternion))                                # get the relative quaternion between the reference IMU quaternion and the ring IMU quaternion
        ringCurlAmount = getCurl(ringToHandQuaternion)                                                                                  # get the curl angle in radians from the quaternion calculated above
        ringAngle = int(ringCurlAmount*180/3.14)                                                                                        # convert the curl angle to degrees
        # remap the angle output in degrees to a value between 0 and 1023: the following calculations were a bit hacky when I implemented them and I didn't document them properly, still, they were based on observations of the outputs and you may be able to reverse engineer an explanation
        if ringAngle <= 0 and ringAngle >= -180:
            ring_axis = int(682 * -ringAngle / 180)
        elif ringAngle <= 180 and ringAngle >= 90:
            ring_axis = int(682 - (341 / 90) * (ringAngle - 180))
        
        ringCurlQuaternion = quaternionFromAngle(ringCurlAmount, 0)                                                                     # create a quaternion that represents just the amount of curl in the x axis
        ringDecurledQuaternion = quaternion_multiply(ringCurlQuaternion, ringQuaternion)                                                # rotate the ringQuaternion by the curl angle in the x axis
        ringDecurledToHandQuaternion = quaternion_multiply(handQuaternion, quaternion_conjugate(ringDecurledQuaternion))                # get the relative quaternion between the reference IMU quaternion and the quaternion representing the ring IMU rotated back by the curl angle
        ringSplayAmount = getSplay(ringDecurledToHandQuaternion)                                                                        # get the splay angle in radians from the quaternion calculated above
        ringSplayAngle = int(ringSplayAmount*180/3.14)                                                                                  # convert the splay angle to degrees
        # finger   min  rest  max
        # ring     -14   -5    14
        if ringSplayAngle <= -5:
            ring_splay_axis = int(512+512*(ringSplayAngle+5)/9.)
        else:
            ring_splay_axis = int(512+512*(ringSplayAngle+5)/21.)
        if ring_splay_axis < 0:
            ring_splay_axis = 0
        elif ring_splay_axis > 1023:
            ring_splay_axis = 1023

    if pinkyActive:
        pinkyQuaternion = Quaternion(bnoPinky.quaternion[3],bnoPinky.quaternion[0],bnoPinky.quaternion[1],bnoPinky.quaternion[2])       # get the pinky IMU quaternion
        pinkyQuaternion = quaternion_multiply(relativeQuaternion, pinkyQuaternion)                                                      # rotate the pinkyQuaternion to be in the coordinate frame where my calculations work
        pinkyToHandQuaternion = quaternion_multiply(handQuaternion, quaternion_conjugate(pinkyQuaternion))                              # get the relative quaternion between the reference IMU quaternion and the pinky IMU quaternion
        pinkyCurlAmount = getCurl(pinkyToHandQuaternion)                                                                                # get the curl angle in radians from the quaternion calculated above
        pinkyAngle = int(pinkyCurlAmount*180/3.14)                                                                                      # convert the curl angle to degrees
        # remap the angle output in degrees to a value between 0 and 1023: the following calculations were a bit hacky when I implemented them and I didn't document them properly, still, they were based on observations of the outputs and you may be able to reverse engineer an explanation
        if pinkyAngle <= 0 and pinkyAngle >= -180:
            pinky_axis = int(682 * -pinkyAngle / 180)
        elif pinkyAngle <= 180 and pinkyAngle >= 90:
            pinky_axis = int(682 - (341 / 90) * (pinkyAngle - 180))
        
        pinkyCurlQuaternion = quaternionFromAngle(pinkyCurlAmount, 0)                                                                   # create a quaternion that represents just the amount of curl in the x axis
        pinkyDecurledQuaternion = quaternion_multiply(pinkyCurlQuaternion, pinkyQuaternion)                                             # rotate the pinkyQuaternion by the curl angle in the x axis
        pinkyDecurledToHandQuaternion = quaternion_multiply(handQuaternion, quaternion_conjugate(pinkyDecurledQuaternion))              # get the relative quaternion between the reference IMU quaternion and the quaternion representing the pinky IMU rotated back by the curl angle
        pinkySplayAmount = getSplay(pinkyDecurledToHandQuaternion)                                                                      # get the splay angle in radians from the quaternion calculated above
        pinkySplayAngle = int(pinkySplayAmount*180/3.14)                                                                                # convert the splay angle to degrees
        # finger   min  rest  max
        # pinky    -40  -25    -2
        if pinkySplayAngle <= -10:
            pinky_splay_axis = int(512+512*(pinkySplayAngle+25)/15.)
        else:
            pinky_splay_axis = int(512+512*(pinkySplayAngle+25)/23.)
        if pinky_splay_axis < 0:
            pinky_splay_axis = 0
        elif pinky_splay_axis > 1023:
            pinky_splay_axis = 1023
    
    #print(str(indexSplayAngle) + " " + str(middleSplayAngle) + " " + str(ringSplayAngle) + " " + str(pinkySplayAngle))
    #print(str(index_splay_axis) + " " + str(middle_splay_axis) + " " + str(ring_splay_axis) + " " + str(pinky_splay_axis))
    
    if thumb_axis == 700:
        thumbCurlUp = False
    elif thumb_axis == 520:
        thumbCurlUp = True
    if index_axis == 700:
        indexCurlUp = False
    elif index_axis == 520:
        indexCurlUp = True
    if middle_axis == 700:
        middleCurlUp = False
    elif middle_axis == 520:
        middleCurlUp = True
    if ring_axis == 700:
        ringCurlUp = False
    elif ring_axis == 520:
        ringCurlUp = True
    if pinky_axis == 700:
        pinkyCurlUp = False
    elif pinky_axis == 520:
        pinkyCurlUp = True

    if thumbCurlUp:
        thumb_axis = thumb_axis + 1
    else:
        thumb_axis = thumb_axis - 1
    if indexCurlUp:
        index_axis = index_axis + 1
    else:
        index_axis = index_axis - 1
    if middleCurlUp:
        middle_axis = middle_axis + 1
    else:
        middle_axis = middle_axis - 1
    if ringCurlUp:
        ring_axis = ring_axis + 1
    else:
        ring_axis = ring_axis - 1
    if pinkyCurlUp:
        pinky_axis = pinky_axis + 1
    else:
        pinky_axis = pinky_axis - 1

    if thumb_splay_axis == 700:
        thumbSplayUp = False
    elif thumb_splay_axis == 520:
        thumbSplayUp = True
    if index_splay_axis == 700:
        indexSplayUp = False
    elif index_splay_axis == 520:
        indexSplayUp = True
    if middle_splay_axis == 700:
        middleSplayUp = False
    elif middle_splay_axis == 520:
        middleSplayUp = True
    if ring_splay_axis == 700:
        ringSplayUp = False
    elif ring_splay_axis == 520:
        ringSplayUp = True
    if pinky_splay_axis == 700:
        pinkySplayUp = False
    elif pinky_splay_axis == 520:
        pinkySplayUp = True

    if thumbSplayUp:
        thumb_splay_axis = thumb_splay_axis + 1
    else:
        thumb_splay_axis = thumb_splay_axis - 1
    if indexSplayUp:
        index_splay_axis = index_splay_axis + 1
    else:
        index_splay_axis = index_splay_axis - 1
    if middleSplayUp:
        middle_splay_axis = middle_splay_axis + 1
    else:
        middle_splay_axis = middle_splay_axis - 1
    if ringSplayUp:
        ring_splay_axis = ring_splay_axis + 1
    else:
        ring_splay_axis = ring_splay_axis - 1
    if pinkySplayUp:
        pinky_splay_axis = pinky_splay_axis + 1
    else:
        pinky_splay_axis = pinky_splay_axis - 1
    
    # I did a lot of tweaking without knowing exactly what was going on, but I compared the original signals from the development board with the ones I generated using the rp2040 PIO, and figured I needed to invert the bit order for the tundra tracker to receive the SPI communication correctly
    # the next few lines take of this inversion and the header construction
    thumb_axis_inverted = 0
    index_axis_inverted = 0
    middle_axis_inverted = 0
    ring_axis_inverted = 0
    pinky_axis_inverted = 0
    thumb_splay_axis_inverted = 0
    index_splay_axis_inverted = 0
    middle_splay_axis_inverted = 0
    ring_splay_axis_inverted = 0
    pinky_splay_axis_inverted = 0
    joystick_x_inverted = 0
    joystick_y_inverted = 0
    for i in range(10):
        bit = (thumb_axis >> i) & 1  # Get the ith bit from the original_value
        thumb_axis_inverted |= (bit << (9 - i))  # Set the bit in the reversed_value
        bit = (index_axis >> i) & 1  # Get the ith bit from the original_value
        index_axis_inverted |= (bit << (9 - i))  # Set the bit in the reversed_value
        bit = (middle_axis >> i) & 1  # Get the ith bit from the original_value
        middle_axis_inverted |= (bit << (9 - i))  # Set the bit in the reversed_value
        bit = (ring_axis >> i) & 1  # Get the ith bit from the original_value
        ring_axis_inverted |= (bit << (9 - i))  # Set the bit in the reversed_value
        bit = (pinky_axis >> i) & 1  # Get the ith bit from the original_value
        pinky_axis_inverted |= (bit << (9 - i))  # Set the bit in the reversed_value
        bit = (thumb_splay_axis >> i) & 1  # Get the ith bit from the original_value
        thumb_splay_axis_inverted |= (bit << (9 - i))  # Set the bit in the reversed_value
        bit = (index_splay_axis >> i) & 1  # Get the ith bit from the original_value
        index_splay_axis_inverted |= (bit << (9 - i))  # Set the bit in the reversed_value
        bit = (middle_splay_axis >> i) & 1  # Get the ith bit from the original_value
        middle_splay_axis_inverted |= (bit << (9 - i))  # Set the bit in the reversed_value
        bit = (ring_splay_axis >> i) & 1  # Get the ith bit from the original_value
        ring_splay_axis_inverted |= (bit << (9 - i))  # Set the bit in the reversed_value
        bit = (pinky_splay_axis >> i) & 1  # Get the ith bit from the original_value
        pinky_splay_axis_inverted |= (bit << (9 - i))  # Set the bit in the reversed_value
        bit = (joystick_x >> i) & 1  # Get the ith bit from the original_value
        joystick_x_inverted |= (bit << (9 - i))  # Set the bit in the reversed_value
        bit = (joystick_y >> i) & 1  # Get the ith bit from the original_value
        joystick_y_inverted |= (bit << (9 - i))  # Set the bit in the reversed_value
    
    first_header_32bits  = (spi_protocol_rev << 24) + (frame_id << 16) + (report_mode << 8) + (status << 0)
    first_data_32_bits  = (thumb_axis_inverted << 22) + (index_axis_inverted << 12) + (middle_axis_inverted << 2) + (ring_axis_inverted >> 8)
    second_data_32_bits  = (ring_axis_inverted << 24) + (pinky_axis_inverted << 14) + (thumb_splay_axis_inverted << 4) + (index_splay_axis_inverted >> 6)
    third_data_32_bits  = (index_splay_axis_inverted << 26) + (middle_splay_axis_inverted << 16) + (ring_splay_axis_inverted << 6) + (pinky_splay_axis_inverted >> 4)
    forth_data_32_bits  = (pinky_splay_axis_inverted << 28) + (joystick_x_inverted << 18) + (joystick_y_inverted << 8) + (joystickIsEnabled << 7)
    #third_data_32_bits  = (index_splay_axis_inverted << 26) + (middle_splay_axis_inverted << 16) + (joystick_x_inverted << 6) + (joystick_y_inverted >> 4)
    #forth_data_32_bits  = (joystick_y_inverted << 28) + (joystick_x_inverted << 18) + (joystick_y_inverted << 8) + (joystickIsEnabled << 7)
    
    byte1 = ((first_data_32_bits >> 24) & 0xFF)
    byte2 = ((first_data_32_bits >> 16) & 0xFF)
    byte3 = ((first_data_32_bits >> 8) & 0xFF)
    byte4 = ((first_data_32_bits >> 0) & 0xFF)
    byte1Inverted = 0
    byte2Inverted = 0
    byte3Inverted = 0
    byte4Inverted = 0
    
    for i in range(8):
        bit = (byte1 >> i) & 1  # Get the ith bit from the original_value
        byte1Inverted |= (bit << (7 - i))  # Set the bit in the reversed_value
        bit = (byte2 >> i) & 1  # Get the ith bit from the original_value
        byte2Inverted |= (bit << (7 - i))  # Set the bit in the reversed_value
        bit = (byte3 >> i) & 1  # Get the ith bit from the original_value
        byte3Inverted |= (bit << (7 - i))  # Set the bit in the reversed_value
        bit = (byte4 >> i) & 1  # Get the ith bit from the original_value
        byte4Inverted |= (bit << (7 - i))  # Set the bit in the reversed_value
    first_data_32_bits  = (byte1Inverted << 24) + (byte2Inverted << 16) + (byte3Inverted << 8) + (byte4Inverted << 0)
    
    byte1 = ((second_data_32_bits >> 24) & 0xFF)
    byte2 = ((second_data_32_bits >> 16) & 0xFF)
    byte3 = ((second_data_32_bits >> 8) & 0xFF)
    byte4 = ((second_data_32_bits >> 0) & 0xFF)
    byte1Inverted = 0
    byte2Inverted = 0
    byte3Inverted = 0
    byte4Inverted = 0
    for i in range(8):
        bit = (byte1 >> i) & 1  # Get the ith bit from the original_value
        byte1Inverted |= (bit << (7 - i))  # Set the bit in the reversed_value
        bit = (byte2 >> i) & 1  # Get the ith bit from the original_value
        byte2Inverted |= (bit << (7 - i))  # Set the bit in the reversed_value
        bit = (byte3 >> i) & 1  # Get the ith bit from the original_value
        byte3Inverted |= (bit << (7 - i))  # Set the bit in the reversed_value
        bit = (byte4 >> i) & 1  # Get the ith bit from the original_value
        byte4Inverted |= (bit << (7 - i))  # Set the bit in the reversed_value
    second_data_32_bits = (byte1Inverted << 24) + (byte2Inverted << 16) + (byte3Inverted << 8) + (byte4Inverted << 0)

    byte1 = ((third_data_32_bits >> 24) & 0xFF)
    byte2 = ((third_data_32_bits >> 16) & 0xFF)
    byte3 = ((third_data_32_bits >> 8) & 0xFF)
    byte4 = ((third_data_32_bits >> 0) & 0xFF)
    byte1Inverted = 0
    byte2Inverted = 0
    byte3Inverted = 0
    byte4Inverted = 0
    for i in range(8):
        bit = (byte1 >> i) & 1  # Get the ith bit from the original_value
        byte1Inverted |= (bit << (7 - i))  # Set the bit in the reversed_value
        bit = (byte2 >> i) & 1  # Get the ith bit from the original_value
        byte2Inverted |= (bit << (7 - i))  # Set the bit in the reversed_value
        bit = (byte3 >> i) & 1  # Get the ith bit from the original_value
        byte3Inverted |= (bit << (7 - i))  # Set the bit in the reversed_value
        bit = (byte4 >> i) & 1  # Get the ith bit from the original_value
        byte4Inverted |= (bit << (7 - i))  # Set the bit in the reversed_value
    third_data_32_bits = (byte1Inverted << 24) + (byte2Inverted << 16) + (byte3Inverted << 8) + (byte4Inverted << 0)
    
    byte1 = ((forth_data_32_bits >> 24) & 0xFF)
    byte2 = ((forth_data_32_bits >> 16) & 0xFF)
    byte3 = ((forth_data_32_bits >> 8) & 0xFF)
    byte4 = ((forth_data_32_bits >> 0) & 0xFF)
    byte1Inverted = 0
    byte2Inverted = 0
    byte3Inverted = 0
    byte4Inverted = 0
    for i in range(8):
        bit = (byte1 >> i) & 1  # Get the ith bit from the original_value
        byte1Inverted |= (bit << (7 - i))  # Set the bit in the reversed_value
        bit = (byte2 >> i) & 1  # Get the ith bit from the original_value
        byte2Inverted |= (bit << (7 - i))  # Set the bit in the reversed_value
        bit = (byte3 >> i) & 1  # Get the ith bit from the original_value
        byte3Inverted |= (bit << (7 - i))  # Set the bit in the reversed_value
        bit = (byte4 >> i) & 1  # Get the ith bit from the original_value
        byte4Inverted |= (bit << (7 - i))  # Set the bit in the reversed_value
    forth_data_32_bits = (byte1Inverted << 24) + (byte2Inverted << 16) + (byte3Inverted << 8) + (byte4Inverted << 0)
    
    fullframe = array.array('L',[first_header_32bits, second_header_32bits, first_data_32_bits, second_data_32_bits, third_data_32_bits, forth_data_32_bits])
    print(fullframe)
    
    sm.write(fullframe)      # write the fullframe to the PIO
    frame_id = frame_id + 1  # increment the frame_id
    if frame_id > 255:       # be sure to keep frame_id below 256 to fit one byte
        frame_id = 0
    #timeEnd = time.monotonic()
    #print(str(timeEnd-timeStart))
